SadeepRathnayaka/EN2160-Electronic-Design-Realization/Enclosure/Concept Enclosure/Sketches/1.jpg

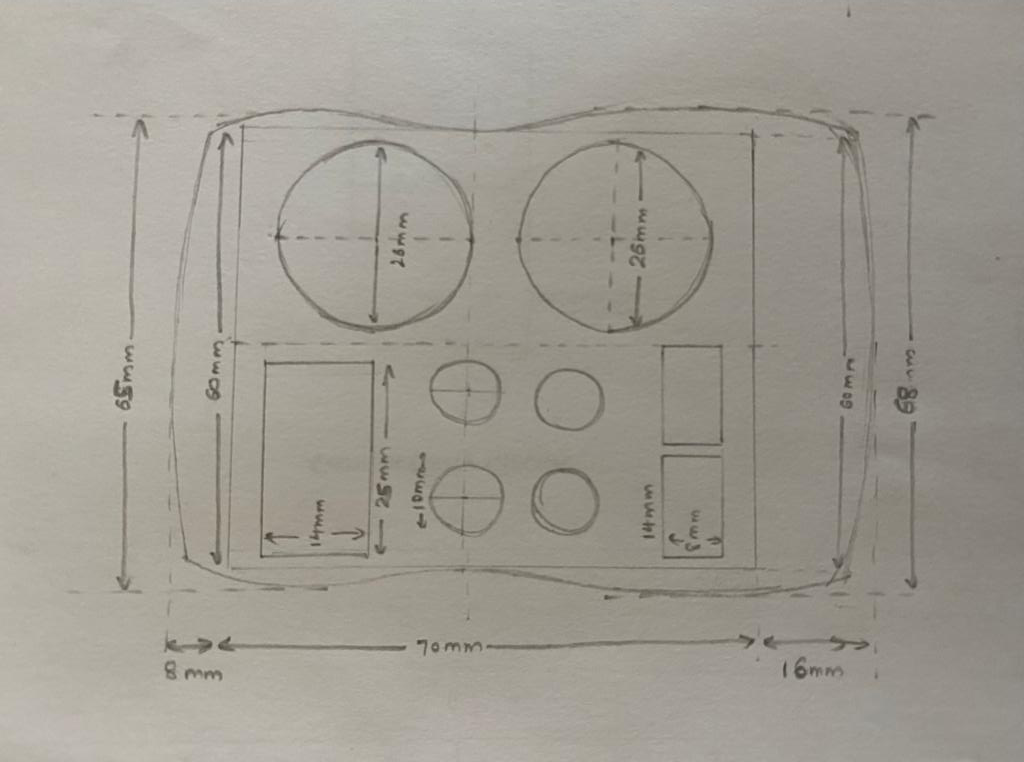
Enclosure/Concept Enclosure/Sketches/1.jpg
