SadeepRathnayaka/EN2160-Electronic-Design-Realization/Enclosure/Concept Enclosure/Sketches/3.jpg

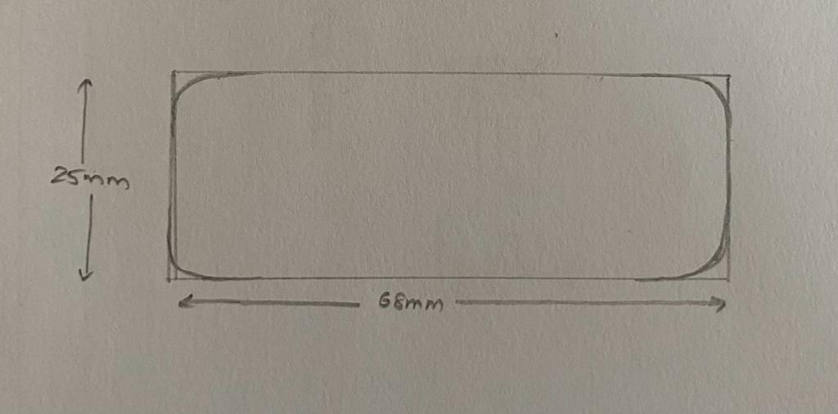
Enclosure/Concept Enclosure/Sketches/3.jpg
