SadeepRathnayaka/EN2160-Electronic-Design-Realization/Images/c checker.png

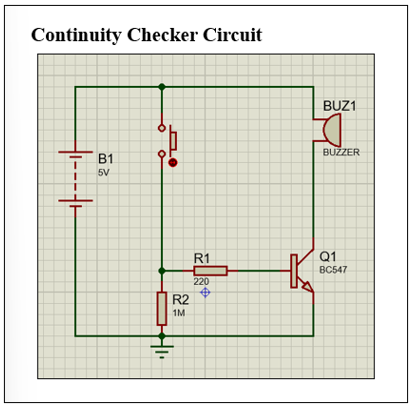
Images/c checker.png
