SadeepRathnayaka/EN2160-Electronic-Design-Realization/Enclosure/Enclosure Design/Parts/4mm-panel-mount-banana-socket/Renderings/4mm Panel Mount Banana Socket20120109-25914-isfw10.JPG

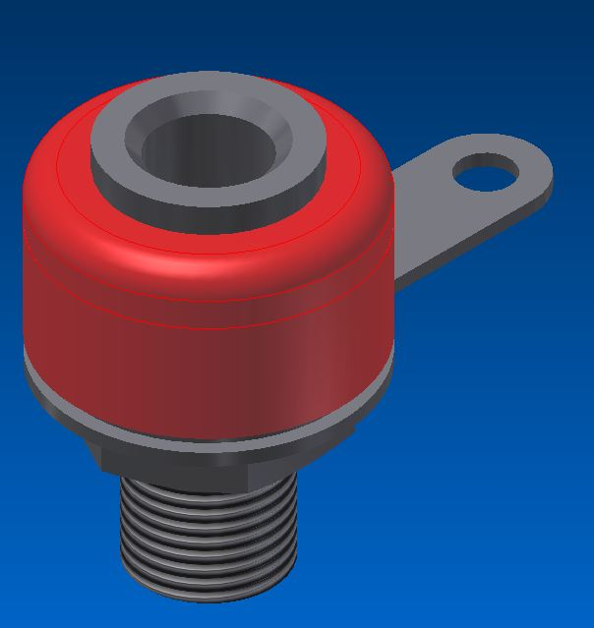
Enclosure/Enclosure Design/Parts/4mm-panel-mount-banana-socket/Renderings/4mm Panel Mount Banana Socket20120109-25914-isfw10.JPG
