SadeepRathnayaka/EN2160-Electronic-Design-Realization/Enclosure/Enclosure Design/Parts/4mm-panel-mount-banana-socket/Renderings/4mm Panel Mount Banana Socket220120109-1214-2uyugb.jpg

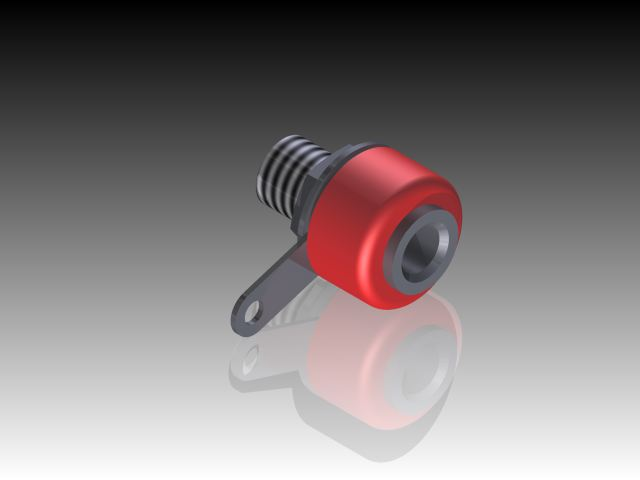
Enclosure/Enclosure Design/Parts/4mm-panel-mount-banana-socket/Renderings/4mm Panel Mount Banana Socket220120109-1214-2uyugb.jpg
