SadeepRathnayaka/EN2160-Electronic-Design-Realization/Enclosure/Enclosure Design/Parts/ina219-dc-current-sensor-1.snapshot.3/CJMCU-219 INA219.png

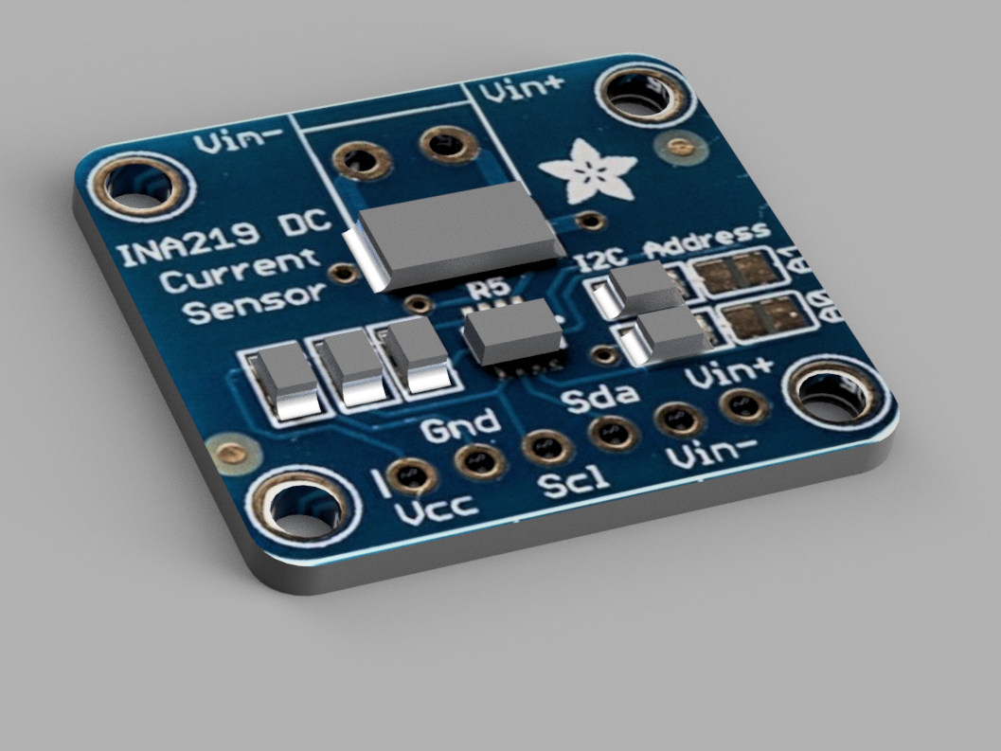
Enclosure/Enclosure Design/Parts/ina219-dc-current-sensor-1.snapshot.3/CJMCU-219 INA219.png
