SadeepRathnayaka/EN2160-Electronic-Design-Realization/Enclosure/Enclosure Design/Parts/tp4056-battery-charger-1.snapshot.2/Nový rastrový obrázek (11).bmp

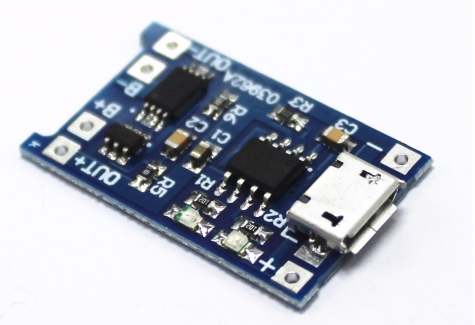
Enclosure/Enclosure Design/Parts/tp4056-battery-charger-1.snapshot.2/Nový rastrový obrázek (11).bmp
