SadeepRathnayaka/EN2160-Electronic-Design-Realization/Enclosure/Enclosure Design/Parts/Power switch/INTERRUPTOR BASCULANTE.STEP

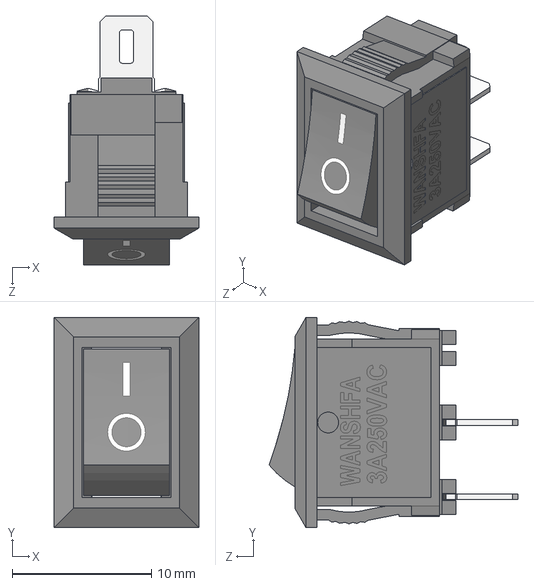
[picture p77: CAD file, 2023-09-06]
Enclosure/Enclosure Design/Parts/Power switch/INTERRUPTOR BASCULANTE.STEP
10.4 x 15.1 x 17.9 mm
