SadeepRathnayaka/EN2160-Electronic-Design-Realization/Enclosure/Enclosure Design/Parts/rocker-switch-25.snapshot.3/RockerSwitch.STEP

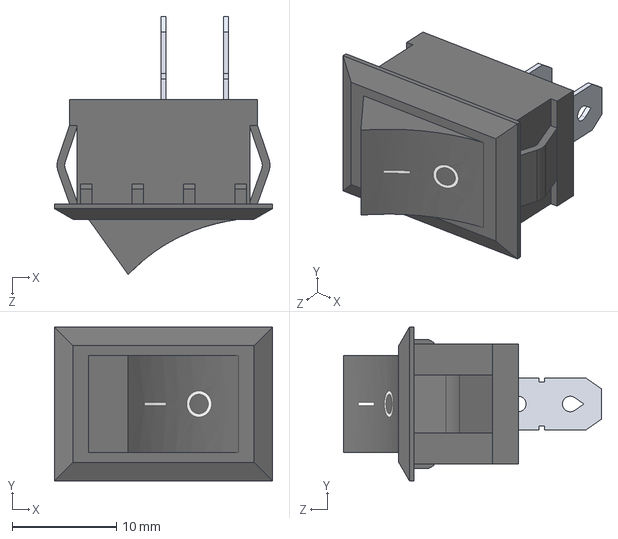
[picture p78: CAD file, 2023-09-06]
Enclosure/Enclosure Design/Parts/rocker-switch-25.snapshot.3/RockerSwitch.STEP
21.0 x 14.8 x 24.8 mm
