SadeepRathnayaka/EN2160-Electronic-Design-Realization/Enclosure/Enclosure Design/Parts/rotary-switch-encoder-3-pole-4-throw-3p4t-1.snapshot.2/Rotary switch 3P4T.step.SLDPRT

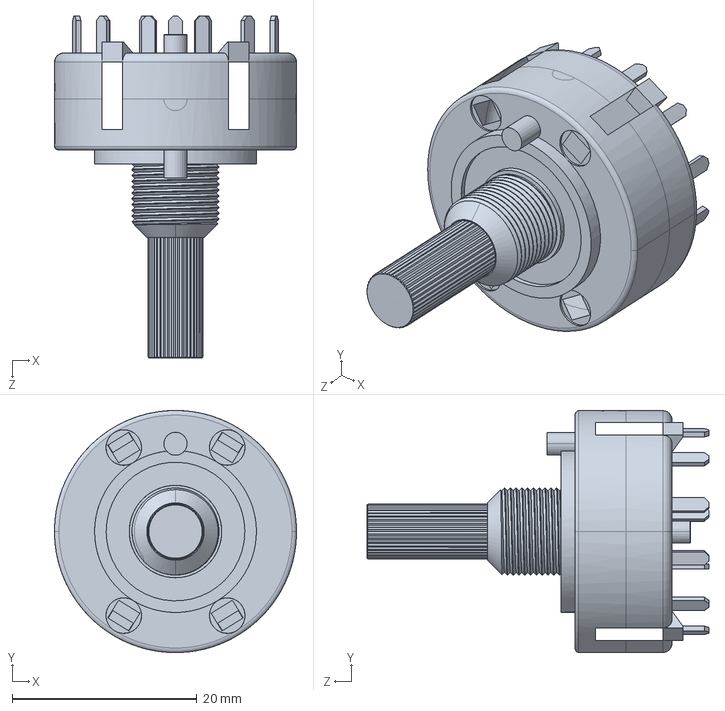
[picture p79: CAD file, 2023-09-06]
Enclosure/Enclosure Design/Parts/rotary-switch-encoder-3-pole-4-throw-3p4t-1.snapshot.2/Rotary switch 3P4T.step.SLDPRT
26.2 x 26.2 x 37.0 mm
