SadeepRathnayaka/EN2160-Electronic-Design-Realization/Enclosure/Enclosure Design/Parts/STDP switch/UTS.MINI ROCKER SWITCH SENA Part.SLDPRT

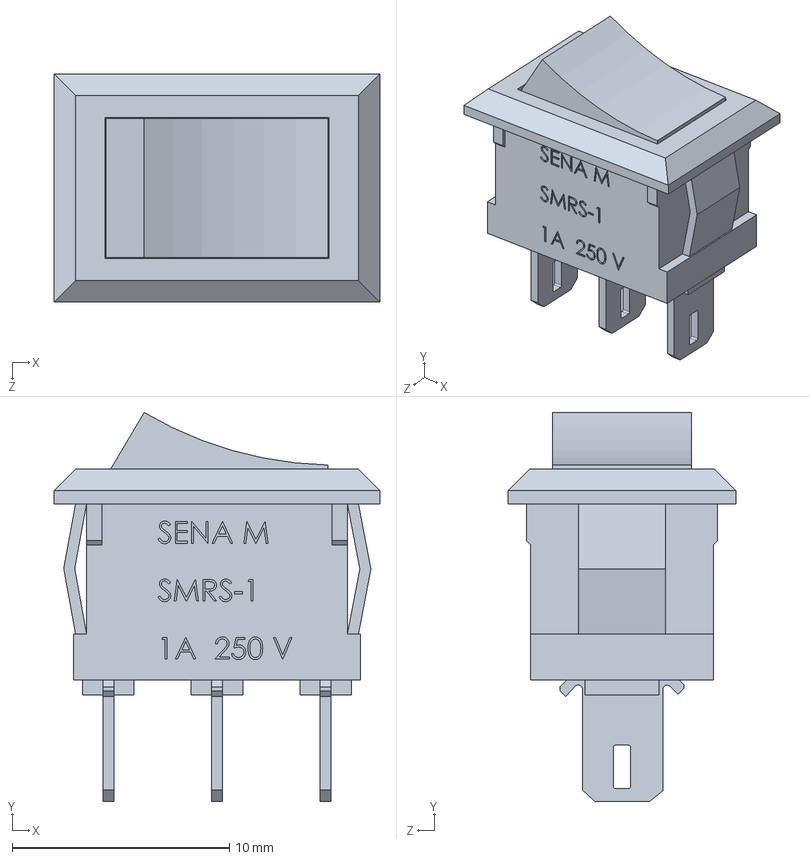
[picture p80: CAD file, 2023-09-06]
Enclosure/Enclosure Design/Parts/STDP switch/UTS.MINI ROCKER SWITCH SENA Part.SLDPRT
15.0 x 17.9 x 10.5 mm
