SadeepRathnayaka/EN2160-Electronic-Design-Realization/Enclosure/Enclosure Design/Parts/tp4056-battery-charger-1.snapshot.2/tp4056 micro usb 18650 charger.SLDPRT

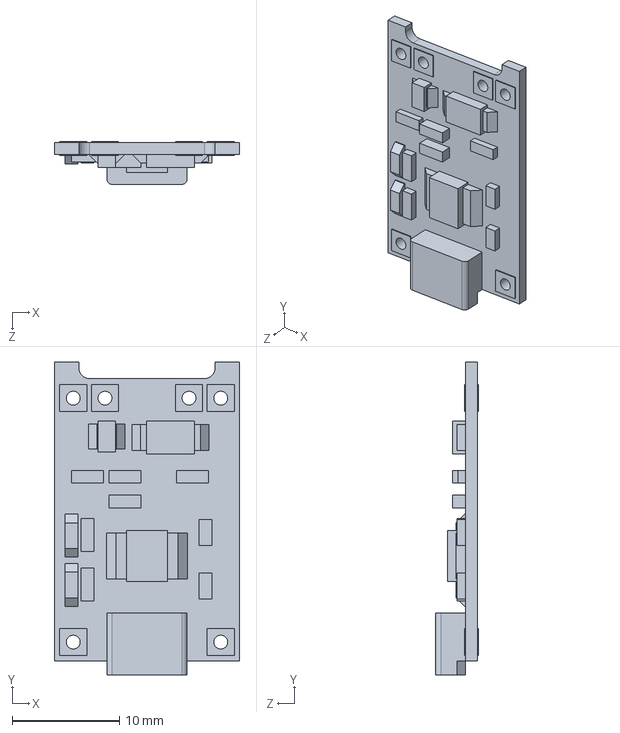
[picture p81: CAD file, 2023-09-06]
Enclosure/Enclosure Design/Parts/tp4056-battery-charger-1.snapshot.2/tp4056 micro usb 18650 charger.SLDPRT
17.3 x 29.2 x 4.00 mm
