SadeepRathnayaka/EN2160-Electronic-Design-Realization/Enclosure/Concept Enclosure/display-oled-ssd1306-de-0-96-1.snapshot.6/Lip and Groove/Groove.SLDPRT

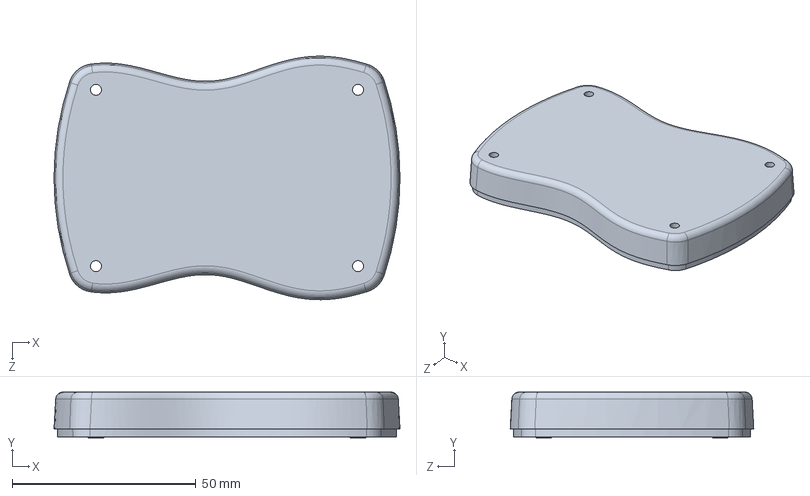
[picture p82: CAD file, 2023-09-06]
Enclosure/Concept Enclosure/display-oled-ssd1306-de-0-96-1.snapshot.6/Lip and Groove/Groove.SLDPRT
94.2 x 12.5 x 66.3 mm
