SadeepRathnayaka/EN2160-Electronic-Design-Realization/Enclosure/Concept Enclosure/display-oled-ssd1306-de-0-96-1.snapshot.6/Part1.SLDPRT

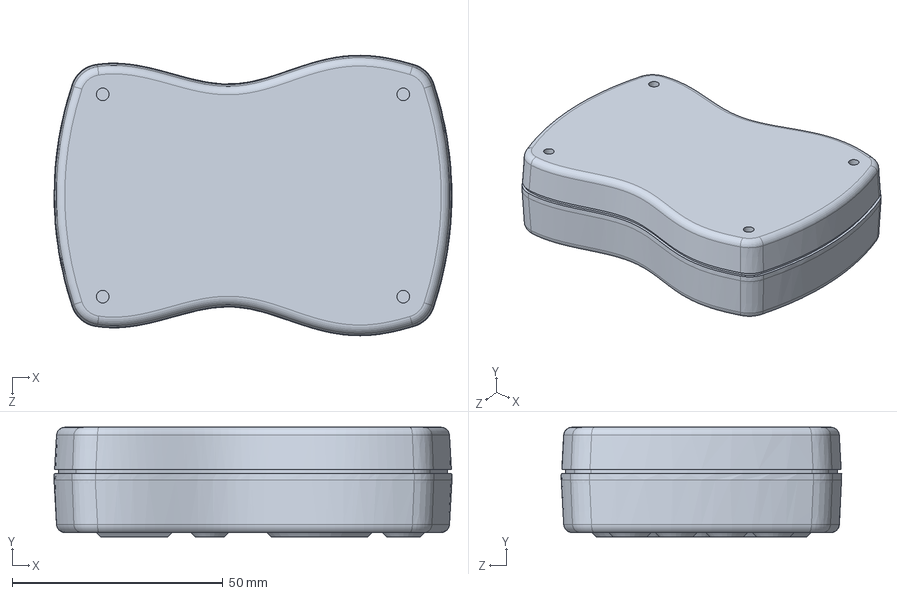
[picture p83: CAD file, 2023-09-06]
Enclosure/Concept Enclosure/display-oled-ssd1306-de-0-96-1.snapshot.6/Part1.SLDPRT
94.4 x 26.0 x 66.6 mm
