SadeepRathnayaka/EN2160-Electronic-Design-Realization/Enclosure/Enclosure Design/Parts/Part2.SLDPRT

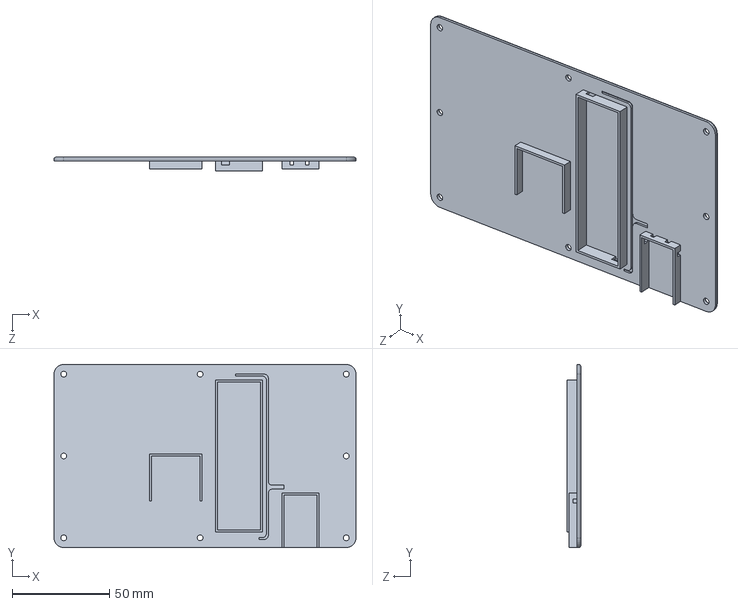
[picture p84: CAD file, 2023-09-06]
Enclosure/Enclosure Design/Parts/Part2.SLDPRT
155.0 x 94.0 x 7.00 mm
