SadeepRathnayaka/EN2160-Electronic-Design-Realization/Enclosure/Enclosure Design/Parts/STDP switch/tugas uts rocker switch.SLDPRT

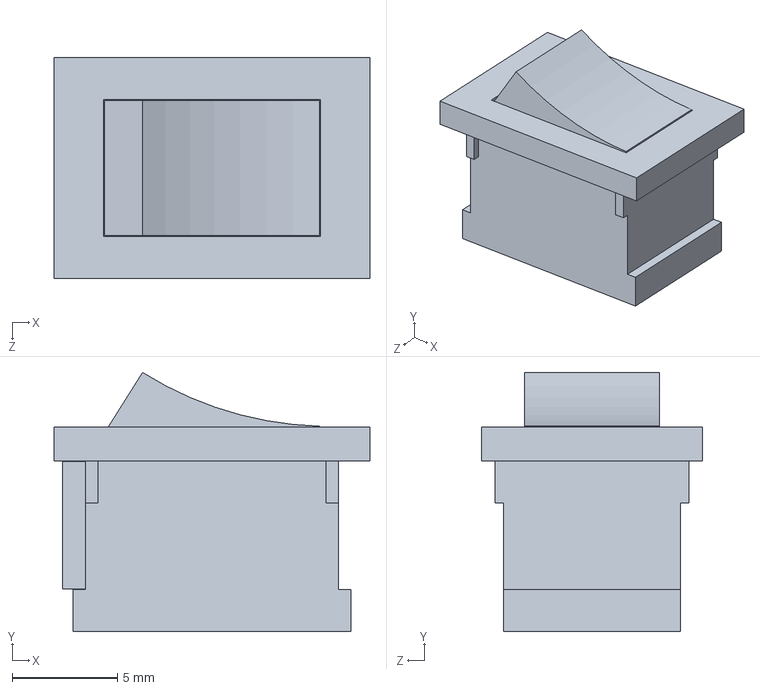
[picture p85: CAD file, 2023-09-06]
Enclosure/Enclosure Design/Parts/STDP switch/tugas uts rocker switch.SLDPRT
15.0 x 12.3 x 10.5 mm
