SadeepRathnayaka/EN2160-Electronic-Design-Realization/Enclosure/Enclosure Design/Finalized/Part2.SLDPRT

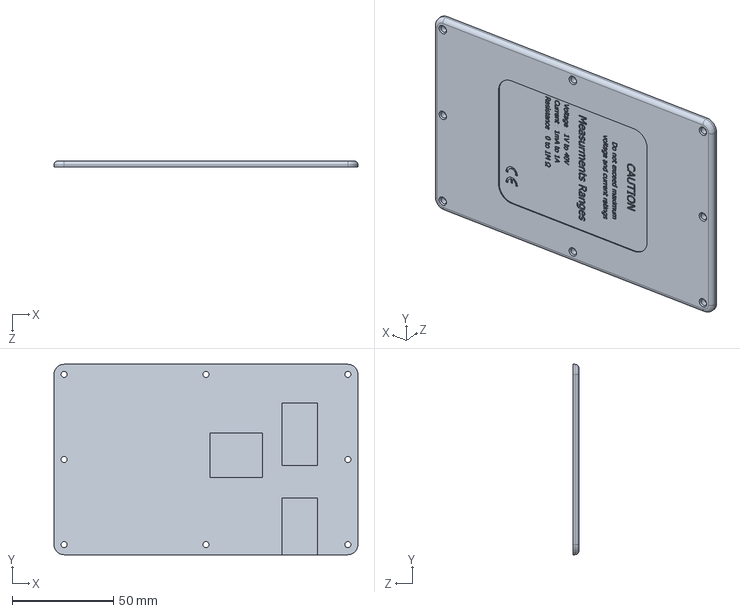
[picture p86: CAD file, 2023-09-06]
Enclosure/Enclosure Design/Finalized/Part2.SLDPRT
150.0 x 94.0 x 3.00 mm
