SadeepRathnayaka/EN2160-Electronic-Design-Realization/Enclosure/Enclosure Design/Parts/tp4056-battery-charger-1.snapshot.2/Part12.SLDPRT

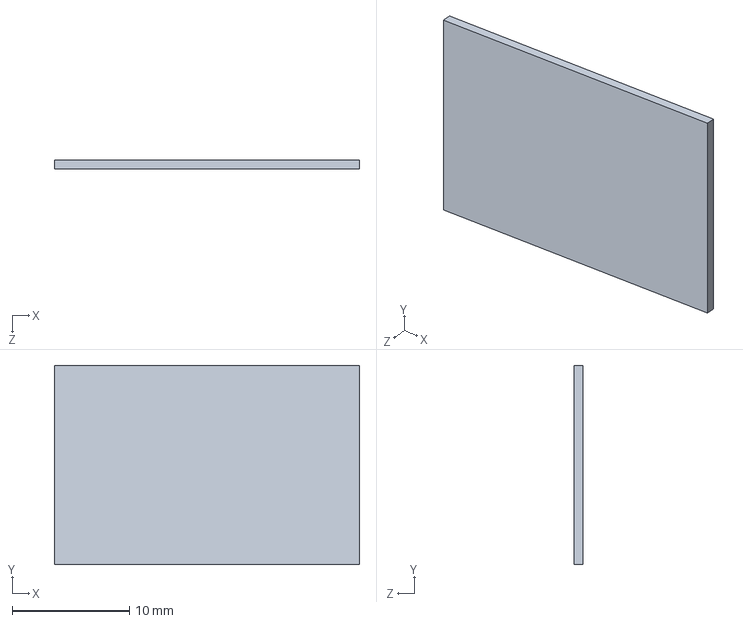
[picture p87: CAD file, 2023-09-06]
Enclosure/Enclosure Design/Parts/tp4056-battery-charger-1.snapshot.2/Part12.SLDPRT
26.0 x 17.0 x 0.8 mm
